oleksiikutuzov/esp32-homekit-led-strip/PCB/ESP32-C3/ESP32-C3_v1.0_TOP.png

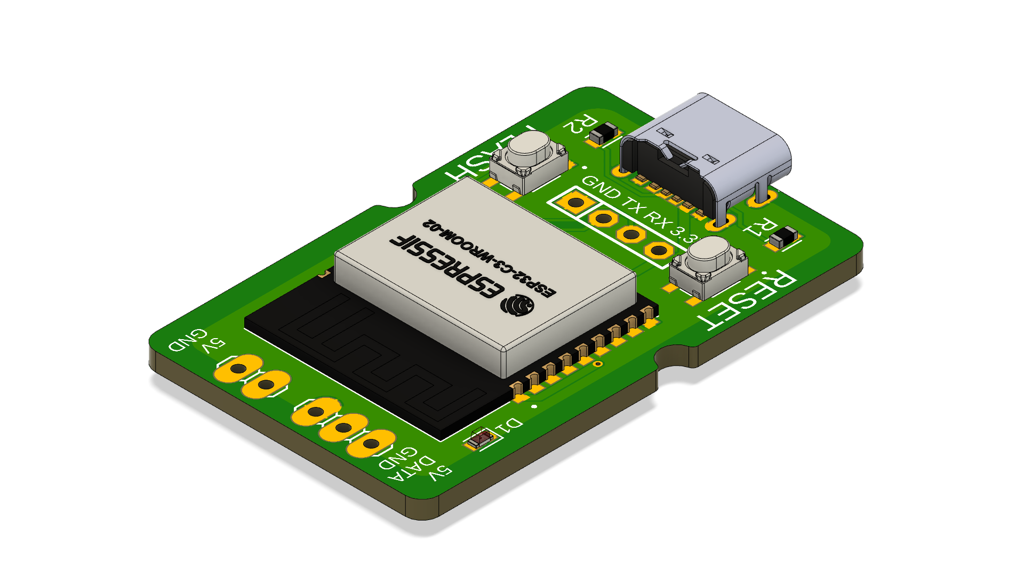
PCB/ESP32-C3/ESP32-C3_v1.0_TOP.png
